j-hoppe/uTracer11/resources/empty-document-page.jpg

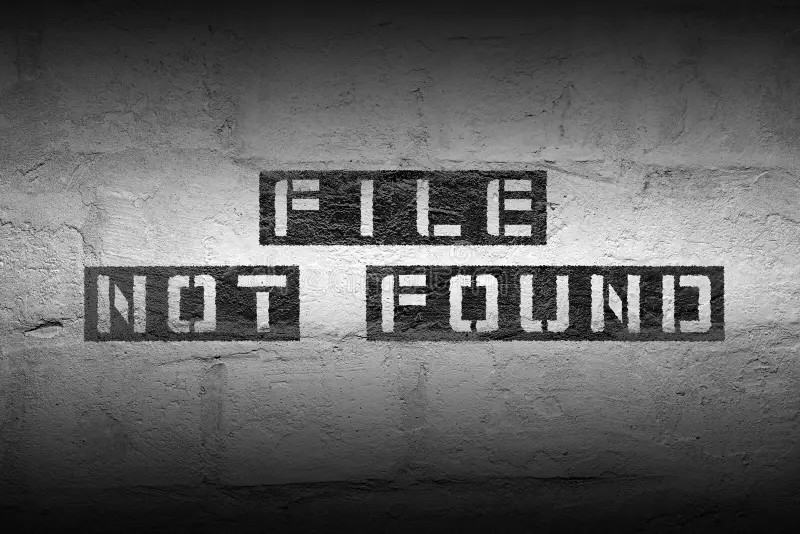
resources/empty-document-page.jpg
