j-hoppe/uTracer11/resources/pdp1134/mp00082-controlword/MP00082-15.jpg

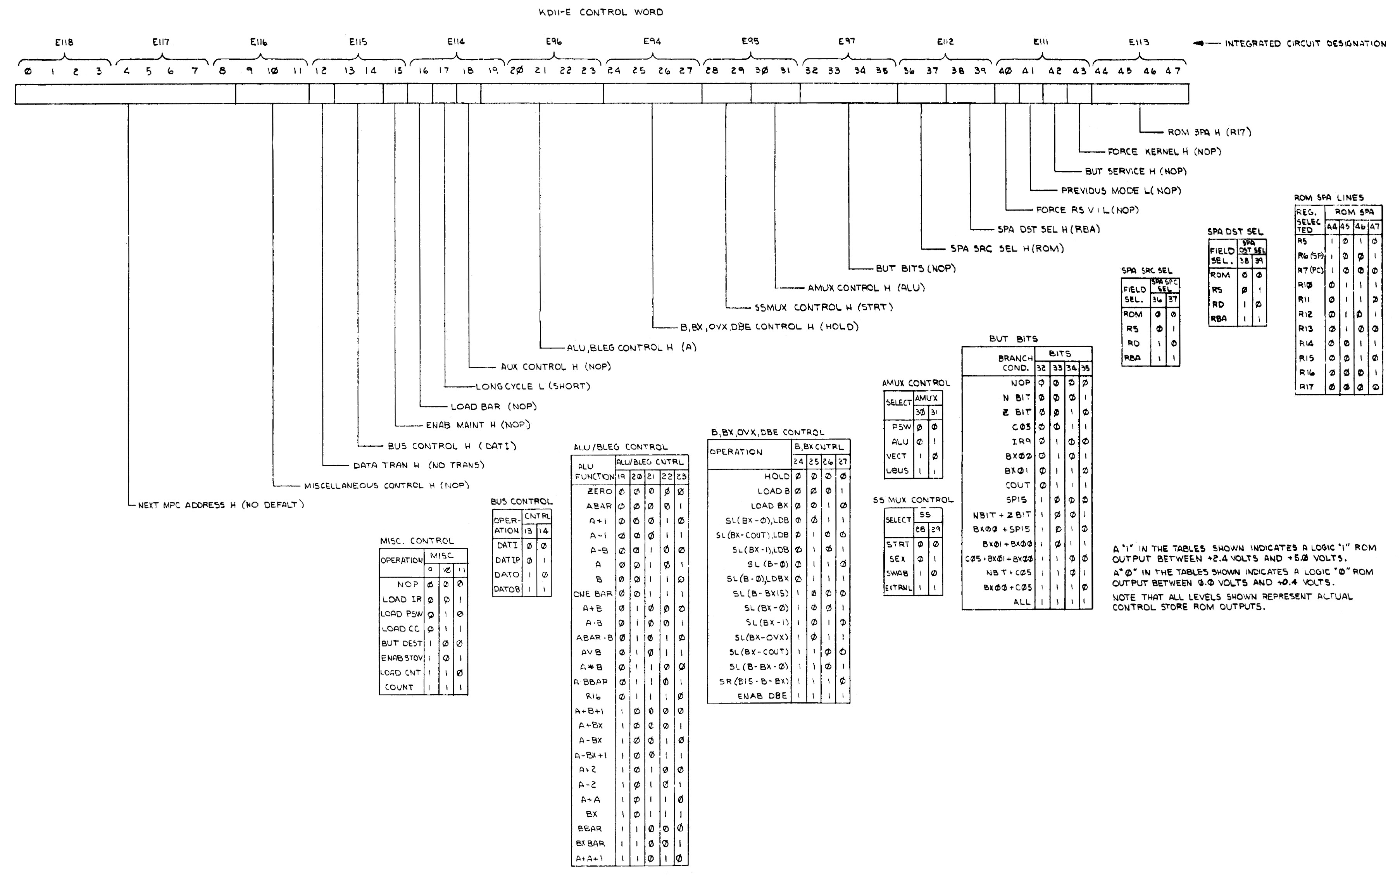
resources/pdp1134/mp00082-controlword/MP00082-15.jpg
