j-hoppe/uTracer11/resources/pdp1134/mp00082-datapath/MP00082-14-extended.jpg

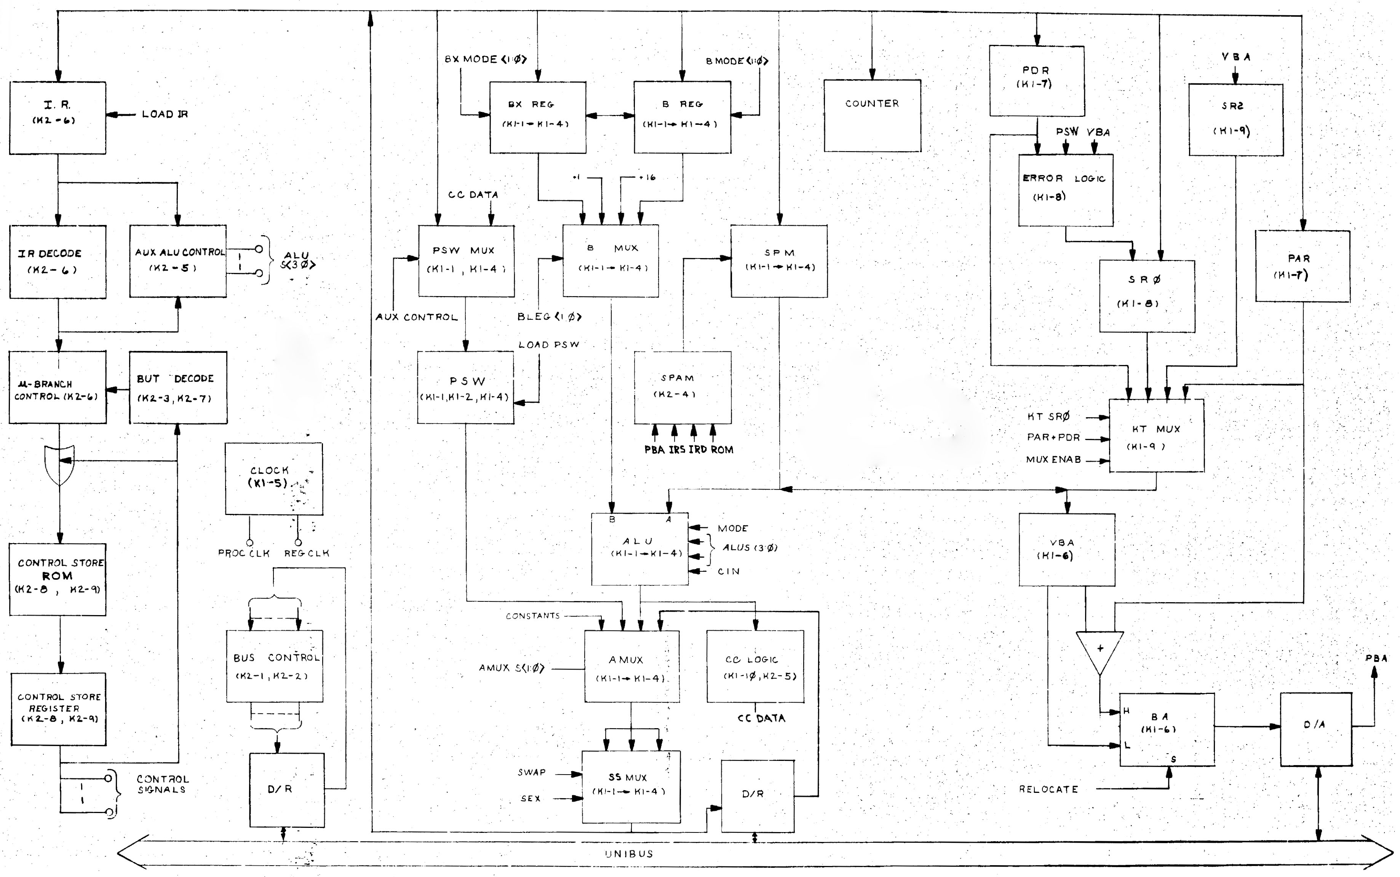
resources/pdp1134/mp00082-datapath/MP00082-14-extended.jpg
