j-hoppe/uTracer11/resources/pdp1134/mp00082-uflow/MP00082-25.jpg

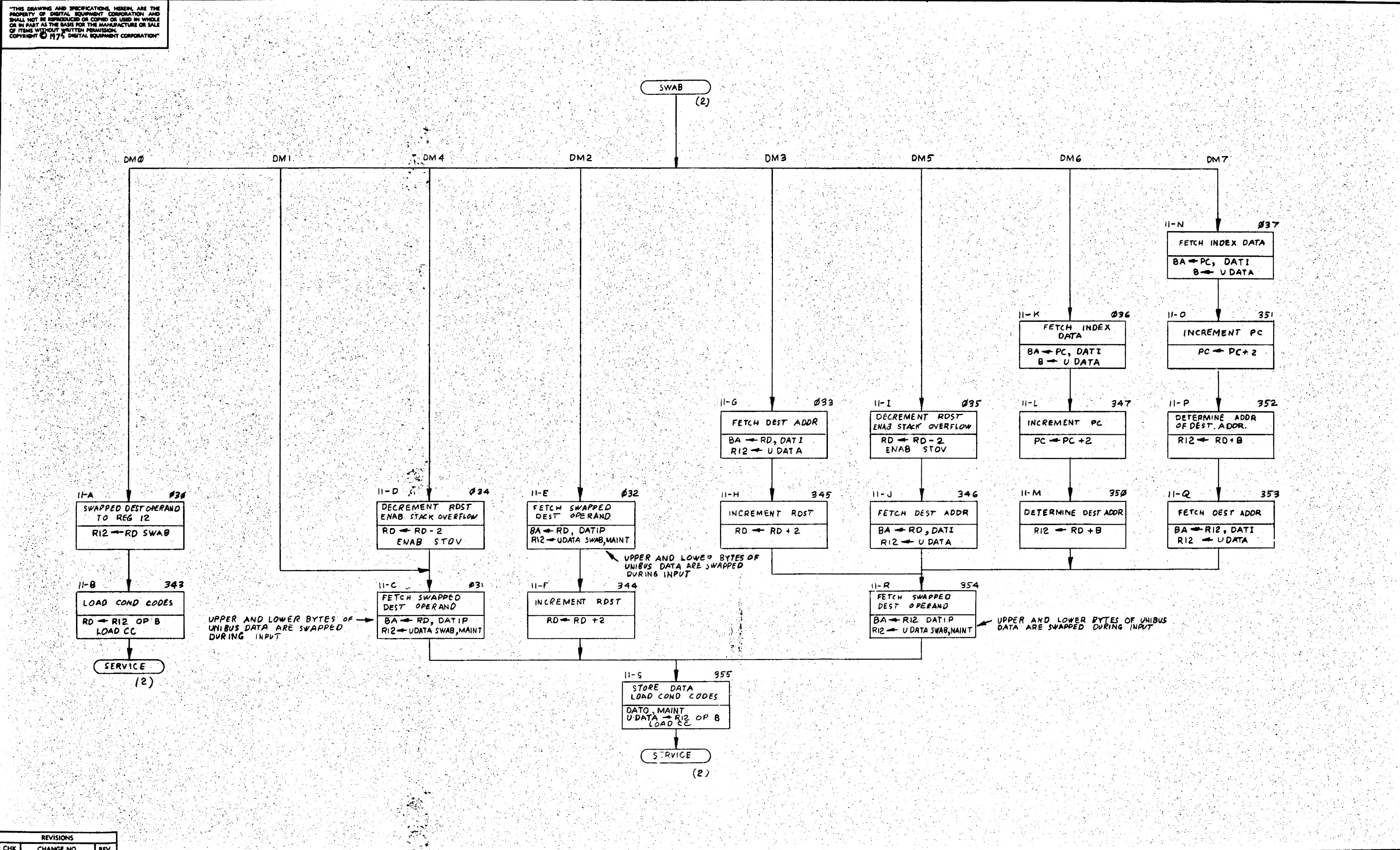
resources/pdp1134/mp00082-uflow/MP00082-25.jpg
