j-hoppe/uTracer11/resources/pdp1140/KD11-A_Processor_Flow_Diagrams/KD11-A_Processor_Flow_Diagrams-2.jpg

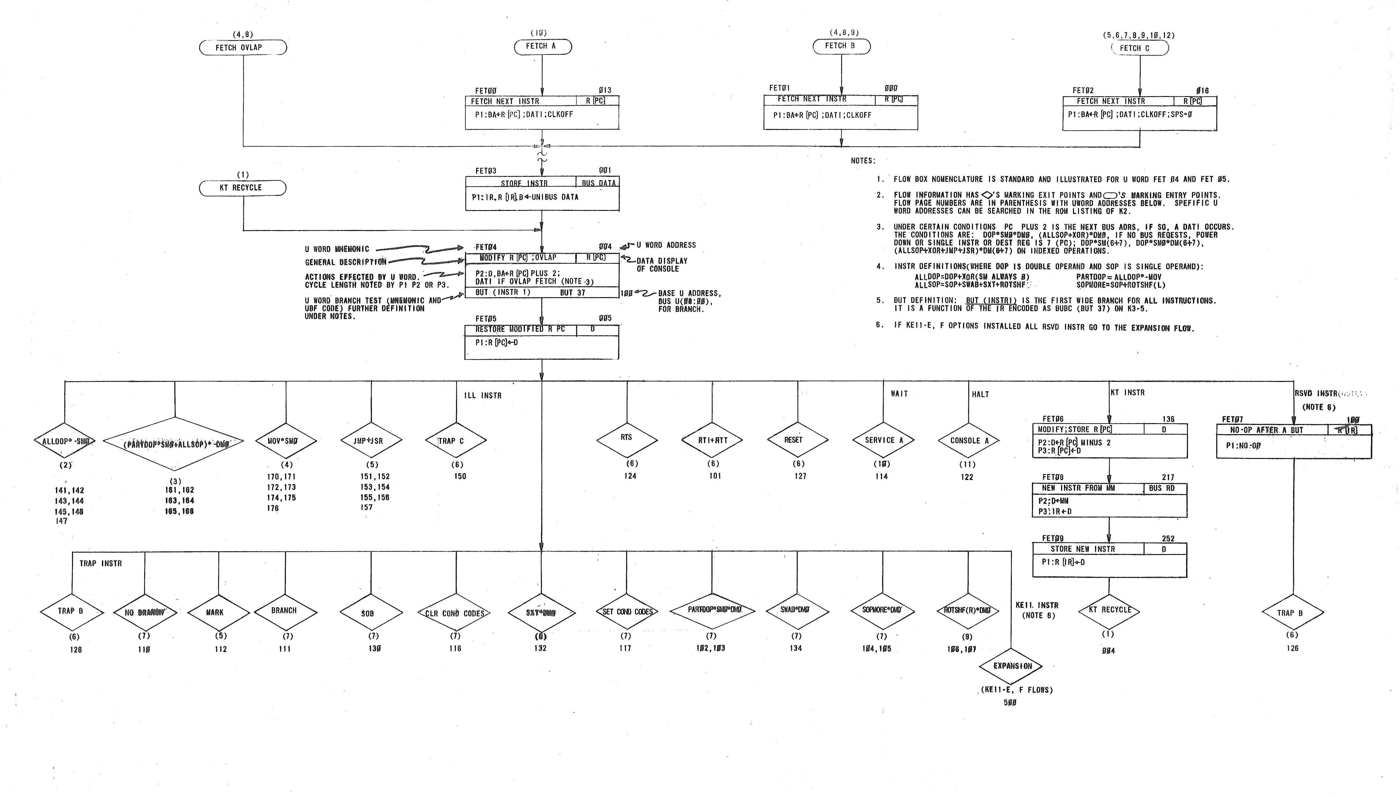
resources/pdp1140/KD11-A_Processor_Flow_Diagrams/KD11-A_Processor_Flow_Diagrams-2.jpg
