j-hoppe/uTracer11/common/pdp1140km11state.h

#include "messages.h"

// Signals exposed o the PDP-11/40 KM11 A and B diagnostic headers
class Pdp1140KM11AState {
public:
    // member variables are exact the labels on DEC 11/40 KM11 overlay sheets
    // inputs from CPU to KM11A
    uint16_t pupp = 0; // not inverted for my convenience
    uint16_t bupp = 0;
    bool trap = 0;
    bool ssyn = 0;
    bool msyn = 0;
    bool t = 0;
    bool c = 0;
    bool v = 0;
    bool z = 0;
    bool n = 0;

    // outputs from KM11A to CPU, physically inverted on M93X2 probe
    // here logically "true" = active

    // "NO MSTOP?", KM11 pin B2, Sheet K4-2
    bool mstop = false; // active: stop micro program execution at mpc set on console switches
    // "MCLK" , KM11 pin U1, sheet K4-2
    bool mclk = false;

    // "MCLK ENABLE" , KM11 pin V2, sheet K4-2
    bool mclk_enab = false;

    // low-level encode/decode
    void inputsFromKM11AResponse(ResponseKM11Signals* respKm11A);
    // GUI sends control signals to PDP11/40 or simulator
    void outputsToKM11AWriteRequest(RequestKM11SignalsWrite* reqKm11A);
    // no outputs over KM11B

    // simulator produces raw KM11 signals
    void inputsToKM11AResponse(ResponseKM11Signals* respKm11A);
    // simulator receives control signals
    void outputsFromKM11AWriteRequest(RequestKM11SignalsWrite* reqKm11A);
}
;

class Pdp1140KM11BState {
	public:
		// member variables are exact the labels on DEC 11/40 KM11 overlay sheets
    // inputs MMU/FPU to KM11B
    uint32_t pba = 0; //17..08
    bool rom_a = 0;
    bool rom_b = 0;
    bool rom_c = 0;
    bool rom_d = 0;
    bool b_15 = 0;
    bool ecin_00 = 0;
    bool exp_unfl = 0;
    bool exp_ovfl = 0;
    bool dr00 = 0;
    bool dr09 = 0;
    bool msr00 = 0;
    bool msr01 = 0;
    bool eps_c = 0;
    bool eps_v = 0;
    bool eps_z = 0;
    bool eps_n = 0;
		
    // GUI evaluates raw KM11 signals from PDP11/40 or simulator
    void inputsFromKM11BResponse(ResponseKM11Signals* respKm11B);
    void inputsToKM11BResponse(ResponseKM11Signals* respKm11B);
};	
