j-hoppe/uTracer11/M93X2probe.pio/src/types.h

#ifndef __UTILS_H__
#define __UTILS_H__

#include <Arduino.h>

// please use only types with well defined bit-width
typedef unsigned long uint32_t;
typedef word uint16_t;
typedef byte uint8_t;

#endif //__UTILS_H__
