j-hoppe/uTracer11/gui/mainframe.cpp

// mainframe - implementation
// main GUI logic here

#include "application.h"
#include "mainframe.h"
#include "wxutils.h"

// the frame provides system with polling clock, defined by Start() in application
void MainFrame::updateTimerOnTimer(wxTimerEvent& event) {
    UNREFERENCED_PARAMETER(event);
    wxGetApp().onTimer(updateTimer.GetInterval());
}

void MainFrame::powerCycleButtonOnButtonClick(wxCommandEvent& event)
{
    UNREFERENCED_PARAMETER(event);
    wxGetApp().pdp11Adapter->powerDown();
    wxGetApp().pdp11Adapter->powerUp();
}

void MainFrame::manClockEnableButtonOnToggleButton(wxCommandEvent& event)
{
    UNREFERENCED_PARAMETER(event);
    wxGetApp().pdp11Adapter->setManClkEnable(manClockEnableButton->GetValue());
}

void MainFrame::microStepButtonOnButtonClick(wxCommandEvent& event)
{
    UNREFERENCED_PARAMETER(event);
    wxGetApp().pdp11Adapter->requestUStep();
}

// load selectde file into textcontrol
void MainFrame::scriptLoadButtonOnButtonClick(wxCommandEvent& event) 
{
    UNREFERENCED_PARAMETER(event);
    wxFileName scriptFilePath = wxGetApp().pdp11Adapter->scriptFilePath; // load prev

    wxFileDialog
        openFileDialog(this, "Load JavaScript file", scriptFilePath.GetPath(), scriptFilePath.GetFullName(),
            "JavaScript files (*.js)|*.js|All files (*.*)|*.*", wxFD_OPEN | wxFD_FILE_MUST_EXIST);

    if (openFileDialog.ShowModal() == wxID_CANCEL)
        return;     // the user changed idea...
    
    wxGetApp().pdp11Adapter->scriptFilePath = openFileDialog.GetPath(); // save for next call

	wxString lines = wxLoadTextFromFile(openFileDialog.GetPath()) ;
	scriptTextCtrlFB->SetValue(lines) ;
}

// save text control to file
void MainFrame::scriptSaveButtonOnButtonClick(wxCommandEvent& event)
{
    UNREFERENCED_PARAMETER(event);
    wxFileName scriptFilePath = wxGetApp().pdp11Adapter->scriptFilePath; // load prev
    wxFileDialog
        saveFileDialog(this, "Save JavaScript file", scriptFilePath.GetPath(), scriptFilePath.GetFullName(),
            "JavaScript files (*.js)|*.js|All files (*.*)|*.*", wxFD_SAVE | wxFD_OVERWRITE_PROMPT);

    if (saveFileDialog.ShowModal() == wxID_CANCEL)
        return;     // the user changed idea...

    wxGetApp().pdp11Adapter->scriptFilePath = saveFileDialog.GetPath(); // save for next call

    // save the current contents in the file;
    wxString lines = scriptTextCtrlFB->GetValue() ;
	wxSaveTextToFile(saveFileDialog.GetPath(), lines) ;
}

void MainFrame::scriptRunButtonOnButtonClick(wxCommandEvent& event) 
 {
	 UNREFERENCED_PARAMETER(event);
	 Pdp11Adapter* pdp11Adapter = wxGetApp().pdp11Adapter;
	 pdp11Adapter->scriptStart() ;
 }

 void MainFrame::scriptAbortButtonOnButtonClick(wxCommandEvent& event) 
{
    UNREFERENCED_PARAMETER(event);
	Pdp11Adapter* pdp11Adapter = wxGetApp().pdp11Adapter;
	pdp11Adapter->scriptAbort() ;
}


void MainFrame::OnShow(wxShowEvent& event) {
    UNREFERENCED_PARAMETER(event);
    // must have a status bar designed
    //SetStatusText(_T("Ready!"));
    //        event.Skip(); 
}

/*
void MainFrame::calcButtonOnButtonClick(wxCommandEvent& event) {

    event.Skip();
}

void MainFrame::saveToClipboardButtonOnButtonClick(wxCommandEvent& event) {
    event.Skip();
}
*/


// on notebook page flip? on show? also on resize?
void Pdp11uFlowPanel::Pdp11uFlowPanelOnPaint(wxPaintEvent& event)
{
    UNREFERENCED_PARAMETER(event);
    Pdp11Adapter* pdp11Adapter = wxGetApp().pdp11Adapter;
    if (pdp11Adapter == nullptr)
        return;
    // reload image and scale
    pdp11Adapter->paintDocumentAnnotations();
}


// painting is slow, check out 
// void wxEvtHandler::CallAfter() 	
// wxFULL_REPAINT_ON_RESIZE 

void Pdp11uFlowPanel::Pdp11uFlowPanelOnSize(wxSizeEvent& event)
{
    UNREFERENCED_PARAMETER(event);
    Pdp11Adapter* pdp11Adapter = wxGetApp().pdp11Adapter;
    if (pdp11Adapter == nullptr)
        return;
    // reload image and scale
    pdp11Adapter->paintDocumentAnnotations();
}


void MemoryPanel::memoryLoadFilePickerOnFileChanged(wxFileDirPickerEvent& event)
{
    UNREFERENCED_PARAMETER(event);
    Pdp11Adapter* pdp11Adapter = wxGetApp().pdp11Adapter;
    // decode combo
    memory_fileformat_t fileFormat = fileformat_none;

    switch (memoryFileFormatComboBox->GetSelection()) {
    case 0: fileFormat = fileformat_addr_value_text; break;
    case 1: fileFormat = fileformat_macro11_listing; break;
    case 2: fileFormat = fileformat_papertape; break;
    }
    if (fileFormat == fileformat_none)
        wxLogError("Invalid File format selected?");
    else
        pdp11Adapter->loadMemoryFile(event.GetPath(), fileFormat);
}

void MemoryPanel::depositMemoryButtonOnButtonClick(wxCommandEvent& event)
{
    UNREFERENCED_PARAMETER(event);
    Pdp11Adapter* pdp11Adapter = wxGetApp().pdp11Adapter;
    pdp11Adapter->depositMemoryImage();
}

void MemoryPanel::manualExamButtonOnButtonClick(wxCommandEvent& event)
{
    UNREFERENCED_PARAMETER(event);
    Pdp11Adapter* pdp11Adapter = wxGetApp().pdp11Adapter;
    uint32_t addr;
    if (!manualExamDepositAddrTextCtrl->GetValue().ToUInt(&addr, 8)) {
        manualExamDepositAddrTextCtrl->SetValue("000000"); // do nothing else
        return;
    }
    addr &= 0x3ffff; // make 18 bit
    pdp11Adapter->singleExam(addr);
    pdp11Adapter->updateManualMemoryExamData = true; // next exam data into edit field
}

void MemoryPanel::manualDepositButtonOnButtonClick(wxCommandEvent& event)
{
    UNREFERENCED_PARAMETER(event);
    Pdp11Adapter* pdp11Adapter = wxGetApp().pdp11Adapter;
    uint32_t addr;
    if (!manualExamDepositAddrTextCtrl->GetValue().ToUInt(&addr, 8)) {
        manualExamDepositAddrTextCtrl->SetValue("000000"); // do nothing else
        return;
    }
    addr &= 0x3ffff; // make 18 bit
    uint32_t data;
    if (!manualExamDepositDataTextCtrl->GetValue().ToUInt(&data, 8)) {
        manualExamDepositDataTextCtrl->SetValue("000000"); // do nothing else
        return;
    }
    pdp11Adapter->singleDeposit(addr, (uint16_t)data);
}

// click into memroy grid: copy addr&data to manual exam/deposit addr&data
void MemoryPanel::memoryGridFBOnGridCellLeftClick(wxGridEvent& event)
{
    UNREFERENCED_PARAMETER(event);
    Pdp11Adapter* pdp11Adapter = wxGetApp().pdp11Adapter;
    pdp11Adapter->onMemoryGridClick(&pdp11Adapter->memoryGridController, event.GetRow(), event.GetCol());
}

void MemoryPanel::ioPageGridFBOnGridCellLeftClick(wxGridEvent& event)
{
    UNREFERENCED_PARAMETER(event);
    Pdp11Adapter* pdp11Adapter = wxGetApp().pdp11Adapter;
    pdp11Adapter->onMemoryGridClick(&pdp11Adapter->ioPageGridController, event.GetRow(), event.GetCol());
}

void MemoryPanel::memoryGridClearButtonFBOnButtonClick(wxCommandEvent& event)
{
    UNREFERENCED_PARAMETER(event);
    Pdp11Adapter* pdp11Adapter = wxGetApp().pdp11Adapter;
    pdp11Adapter->clearMemoryImage(&pdp11Adapter->memoryGridController);
}

void MemoryPanel::ioPageGridClearButtonFBOnButtonClick(wxCommandEvent& event)
{
    UNREFERENCED_PARAMETER(event);
    Pdp11Adapter* pdp11Adapter = wxGetApp().pdp11Adapter;
    pdp11Adapter->clearMemoryImage(&pdp11Adapter->ioPageGridController);
}


void Pdp1134ControlwordPanel::Pdp11uWordPanelOnPaint(wxPaintEvent& event)
{
    UNREFERENCED_PARAMETER(event);
    Pdp11Adapter* pdp11Adapter = wxGetApp().pdp11Adapter;
    if (pdp11Adapter == nullptr)
        return;
    // reload image and scale
    pdp11Adapter->paintDocumentAnnotations();
}

void Pdp1134ControlwordPanel::Pdp11uWordPanelOnSize(wxSizeEvent& event)
{
    UNREFERENCED_PARAMETER(event);
    Pdp11Adapter* pdp11Adapter = wxGetApp().pdp11Adapter;
    if (pdp11Adapter == nullptr)
        return;
    // reload image and scale
    pdp11Adapter->paintDocumentAnnotations();
}


void Pdp1134DataPathPanel::Pdp11DataPathPanelOnPaint(wxPaintEvent& event)
{
    UNREFERENCED_PARAMETER(event);
    Pdp11Adapter* pdp11Adapter = wxGetApp().pdp11Adapter;
    if (pdp11Adapter == nullptr)
        return;
    // reload image and scale
    pdp11Adapter->paintDocumentAnnotations();
}

void Pdp1134DataPathPanel::Pdp11DataPathPanelOnSize(wxSizeEvent& event)
{
    UNREFERENCED_PARAMETER(event);
    Pdp11Adapter* pdp11Adapter = wxGetApp().pdp11Adapter;
    if (pdp11Adapter == nullptr)
        return;
    // reload image and scale
    pdp11Adapter->paintDocumentAnnotations();
}


void TracePanel::traceClearButtonOnButtonClick(wxCommandEvent& event)
{
    UNREFERENCED_PARAMETER(event);
    Pdp11Adapter* pdp11Adapter = wxGetApp().pdp11Adapter;
    pdp11Adapter->traceController.clear();
    //    pdp11Adapter->clearTraceMemoryImage(&pdp11Adapter->ioPageGridController);
}

void TracePanel::traceToClipboardButtonOnButtonClick(wxCommandEvent& event)
{
    UNREFERENCED_PARAMETER(event);
    Pdp11Adapter* pdp11Adapter = wxGetApp().pdp11Adapter;
    pdp11Adapter->traceController.gridToClipboard();
}

// trace grid to max width
void TracePanel::TracePanelFBOnSize(wxSizeEvent& event) {
    UNREFERENCED_PARAMETER(event);
    // adapt the width of the grid to the parent panel, leave the height generated by sizer
    auto w = GetClientRect().width - wxSYS_VSCROLL_X;
    auto h = GetSize().GetHeight() - wxSYS_HSCROLL_Y;
    //traceGridFB->SetMinSize(wxSize(w, h));
    traceGridFB->SetSize(wxSize(w, h));
    //traceGridFB->SetColSize(0, 300);
    traceGridFB->AutoSizeColumns();
    traceGridFB->ForceRefresh();
}
